yogabprawira/jam-digital-masjid/code/DataJadwalSholat.h

/*
 *	Nama File 	:	DataJadwalSholat.h
 *	Deskripsi	: 	Library untuk menerjemahkan data bit jadwal sholat dari eeprom menjadi format waktu
 */

#ifndef _DATAJADWALSHOLAT_h
#define _DATAJADWALSHOLAT_h

#if defined(ARDUINO) && ARDUINO >= 100
	#include "arduino.h"
#else
	#include "WProgram.h"
#endif

#define JANUARI 1
#define FEBRUARI 2
#define MARET 3
#define APRIL 4
#define MEI 5
#define JUNI 6
#define JULI 7
#define AGUSTUS 8
#define SEPTEMBER 9
#define OKTOBER 10
#define NOVEMBER 11
#define DESEMBER 12

class DataJadwalSholat
{
 public:
	 uint8_t jamImsyak(uint8_t tanggal, uint8_t bulan);
	 uint8_t jamSubuh(uint8_t tanggal, uint8_t bulan);
	 uint8_t jamDzuhur(uint8_t tanggal, uint8_t bulan);
	 uint8_t jamAsar(uint8_t tanggal, uint8_t bulan);
	 uint8_t jamMaghrib(uint8_t tanggal, uint8_t bulan);
	 uint8_t jamIsya(uint8_t tanggal, uint8_t bulan);
	 uint8_t menitImsyak(uint8_t tanggal, uint8_t bulan);
	 uint8_t menitSubuh(uint8_t tanggal, uint8_t bulan);
	 uint8_t menitDzuhur(uint8_t tanggal, uint8_t bulan);
	 uint8_t menitAsar(uint8_t tanggal, uint8_t bulan);
	 uint8_t menitMaghrib(uint8_t tanggal, uint8_t bulan);
	 uint8_t menitIsya(uint8_t tanggal, uint8_t bulan);
	 
	 /*const byte januari[31][6] = {
		 { 0x31,	0x3B,	0x2A,	0x89,	0x3B,	0x8F },
		 { 0x32,	0x80,	0x2A,	0x89,	0x3B,	0x90 },
		 { 0x32,	0x80,	0x2B,	0x89,	0x3B,	0x90 },
		 { 0x33,	0x81,	0x2B,	0x8A,	0x80,	0x90 },
		 { 0x33,	0x81,	0x2C,	0x8A,	0x80,	0x91 },
		 { 0x34,	0x82,	0x2C,	0x8A,	0x81,	0x91 },
		 { 0x35,	0x83,	0x2C,	0x8B,	0x81,	0x91 },
		 { 0x35,	0x83,	0x2D,	0x8B,	0x81,	0x91 },
		 { 0x36,	0x84,	0x2D,	0x8B,	0x82,	0x92 },
		 { 0x36,	0x84,	0x2E,	0x8C,	0x82,	0x92 },
		 { 0x37,	0x85,	0x2E,	0x8C,	0x82,	0x92 },
		 { 0x38,	0x86,	0x2F,	0x8C,	0x83,	0x92 },
		 { 0x38,	0x86,	0x2F,	0x8C,	0x83,	0x93 },
		 { 0x39,	0x87,	0x2F,	0x8C,	0x83,	0x93 },
		 { 0x39,	0x87,	0x30,	0x8D,	0x83,	0x93 },
		 { 0x3A,	0x88,	0x30,	0x8D,	0x84,	0x93 },
		 { 0x3B,	0x89,	0x30,	0x8D,	0x84,	0x93 },
		 { 0x3B,	0x89,	0x31,	0x8D,	0x84,	0x93 },
		 { 0x80,	0x8A,	0x31,	0x8D,	0x84,	0x93 },
		 { 0x80,	0x8A,	0x31,	0x8D,	0x84,	0x93 },
		 { 0x81,	0x8B,	0x32,	0x8D,	0x85,	0x93 },
		 { 0x82,	0x8C,	0x32,	0x8D,	0x85,	0x93 },
		 { 0x82,	0x8C,	0x32,	0x8D,	0x85,	0x93 },
		 { 0x83,	0x8D,	0x32,	0x8D,	0x85,	0x93 },
		 { 0x83,	0x8D,	0x33,	0x8D,	0x85,	0x93 },
		 { 0x84,	0x8E,	0x33,	0x8D,	0x85,	0x93 },
		 { 0x84,	0x8E,	0x33,	0x8D,	0x85,	0x93 },
		 { 0x85,	0x8F,	0x33,	0x8C,	0x85,	0x93 },
		 { 0x85,	0x8F,	0x34,	0x8C,	0x85,	0x93 },
		 { 0x86,	0x90,	0x34,	0x8C,	0x85,	0x93 },
		 { 0x86,	0x90,	0x34,	0x8C,	0x85,	0x93 }
	 };*/
	 
	 /*const byte februari[31][6] = {
		 { 0x87,	0x91,	0x34,	0x8C,	0x85,	0x93 },
		 { 0x87,	0x91,	0x34,	0x8B,	0x85,	0x92 },
		 { 0x88,	0x92,	0x34,	0x8B,	0x85,	0x92 },
		 { 0x88,	0x92,	0x34,	0x8B,	0x85,	0x92 },
		 { 0x88,	0x92,	0x35,	0x8A,	0x85,	0x92 },
		 { 0x89,	0x93,	0x35,	0x8A,	0x85,	0x92 },
		 { 0x89,	0x93,	0x35,	0x8A,	0x85,	0x91 },
		 { 0x8A,	0x94,	0x35,	0x89,	0x85,	0x91 },
		 { 0x8A,	0x94,	0x35,	0x89,	0x85,	0x91 },
		 { 0x8A,	0x94,	0x35,	0x88,	0x84,	0x91 },
		 { 0x8B,	0x95,	0x35,	0x88,	0x84,	0x90 },
		 { 0x8B,	0x95,	0x35,	0x87,	0x84,	0x90 },
		 { 0x8B,	0x95,	0x35,	0x86,	0x84,	0x90 },
		 { 0x8C,	0x96,	0x35,	0x86,	0x84,	0x8F },
		 { 0x8C,	0x96,	0x35,	0x85,	0x83,	0x8F },
		 { 0x8C,	0x96,	0x35,	0x85,	0x83,	0x8F },
		 { 0x8D,	0x97,	0x35,	0x84,	0x83,	0x8E },
		 { 0x8D,	0x97,	0x35,	0x83,	0x83,	0x8E },
		 { 0x8D,	0x97,	0x35,	0x82,	0x82,	0x8D },
		 { 0x8D,	0x97,	0x35,	0x82,	0x82,	0x8D },
		 { 0x8E,	0x98,	0x34,	0x81,	0x82,	0x8D },
		 { 0x8E,	0x98,	0x34,	0x80,	0x81,	0x8C },
		 { 0x8E,	0x98,	0x34,	0x3B,	0x81,	0x8C },
		 { 0x8E,	0x98,	0x34,	0x3A,	0x81,	0x8B },
		 { 0x8E,	0x98,	0x34,	0x39,	0x80,	0x8B },
		 { 0x8F,	0x99,	0x34,	0x39,	0x80,	0x8A },
		 { 0x8F,	0x99,	0x34,	0x38,	0x80,	0x8A },
		 { 0x8F,	0x99,	0x33,	0x37,	0x3B,	0x8A },
		 { 0x8F,	0x99,	0x33,	0x36,	0x3B,	0x89 },
		 { 0x00,	0x00,	0x00,	0x00,	0x00,	0x00 },
		 { 0x00,	0x00,	0x00,	0x00,	0x00,	0x00 }
	 };*/
	 
	 /*const byte maret[31][6] = {
		 { 0x8F,	0x99,	0x33,	0x35,	0x3A,	0x89 },
		 { 0x8F,	0x99,	0x33,	0x35,	0x3A,	0x88 },
		 { 0x8F,	0x99,	0x33,	0x36,	0x3A,	0x88 },
		 { 0x8F,	0x99,	0x32,	0x36,	0x39,	0x87 },
		 { 0x8F,	0x99,	0x32,	0x37,	0x39,	0x87 },
		 { 0x90,	0x9A,	0x32,	0x37,	0x38,	0x86 },
		 { 0x90,	0x9A,	0x32,	0x37,	0x38,	0x86 },
		 { 0x90,	0x9A,	0x32,	0x38,	0x37,	0x85 },
		 { 0x90,	0x9A,	0x31,	0x38,	0x37,	0x85 },
		 { 0x90,	0x9A,	0x31,	0x38,	0x36,	0x84 },
		 { 0x90,	0x9A,	0x31,	0x39,	0x36,	0x84 },
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
		 { 0x2F,	0x39,	0x28,	0x87,	0x39,	0x8D },
		 { 0x2F,	0x39,	0x28,	0x87,	0x39,	0x8E },
		 { 0x30,	0x3A,	0x29,	0x88,	0x3A,	0x8E },
		 { 0x30,	0x3A,	0x29,	0x88,	0x3A,	0x8F },
		 { 0x31,	0x3B,	0x2A,	0x89,	0x3B,	0x8F }
	 };*/
};

extern DataJadwalSholat jadwalSholat;

#endif
