yogabprawira/jam-digital-masjid/code/Kalibrasi.h

/*
 *	Nama File 	:	Kalibrasi.h
 *	Deskripsi	: 	Library untuk masuk ke mode kalibrasi.
 */

#ifndef _KALIBRASI_h
#define _KALIBRASI_h

#if defined(ARDUINO) && ARDUINO >= 100
	#include "arduino.h"
#else
	#include "WProgram.h"
#endif

class Kalibrasi
{

};

#endif
